zumatt/diplab.github.io/diplab-app/alphaVersion/assets/android-chrome-192x192.png

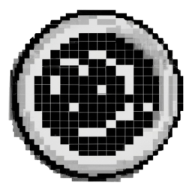
diplab-app/alphaVersion/assets/android-chrome-192x192.png
