zumatt/diplab.github.io/software/DiPLab_Arduino_v01/data/assets/images/eschericaColi_sem_STEVE-GSCHMEISSNER_SCIENCE-PHOTO-LIBRARY.png

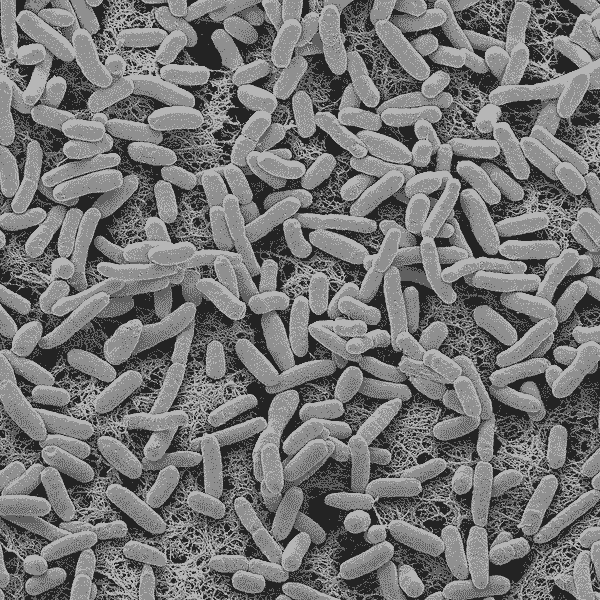
software/DiPLab_Arduino_v01/data/assets/images/eschericaColi_sem_STEVE-GSCHMEISSNER_SCIENCE-PHOTO-LIBRARY.png
