zumatt/diplab.github.io/software/DiPLab_Arduino_v01/data/assets/images/Staphilococcus_sem_SCIENCE-PHOTO-LIBRARY.png

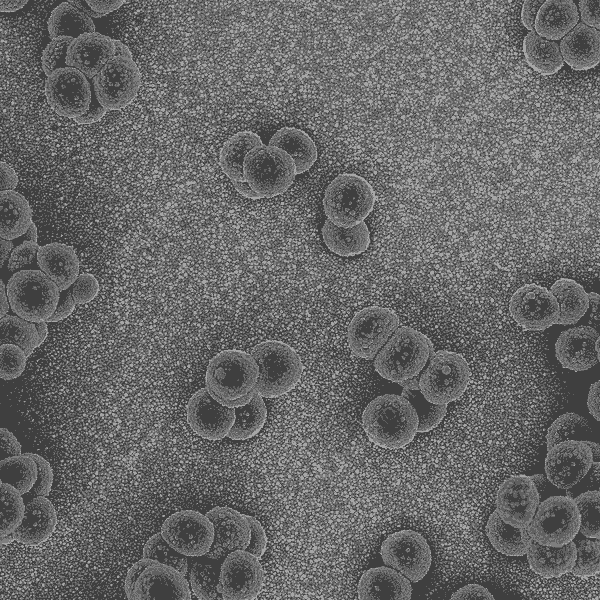
software/DiPLab_Arduino_v01/data/assets/images/Staphilococcus_sem_SCIENCE-PHOTO-LIBRARY.png
