zumatt/diplab.github.io/software/DiPLab_Arduino_v01/data/assets/images/Streptococcus_sem_DENNIS-KUNKEL-MICROSCOPY_SCIENCE-PHOTO-LIBRARY.png

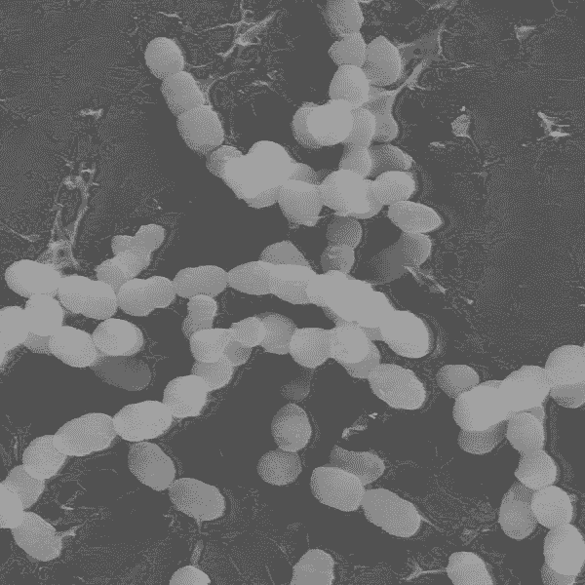
software/DiPLab_Arduino_v01/data/assets/images/Streptococcus_sem_DENNIS-KUNKEL-MICROSCOPY_SCIENCE-PHOTO-LIBRARY.png
